spencer-uk/DubaiXTClone/pictures/image_005.jpg

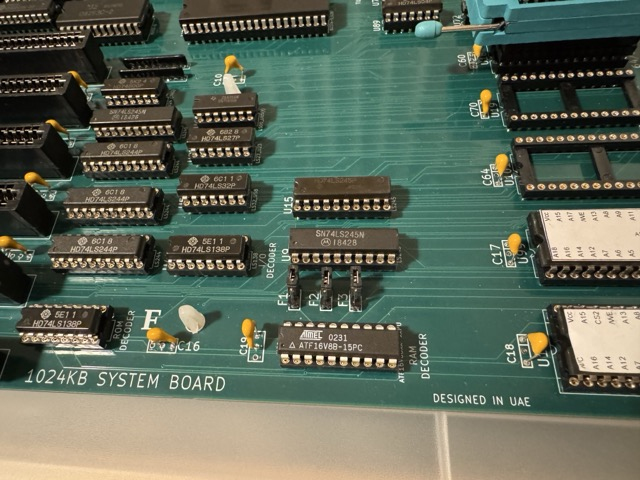
pictures/image_005.jpg
