spencer-uk/DubaiXTClone/pictures/image_008.jpg

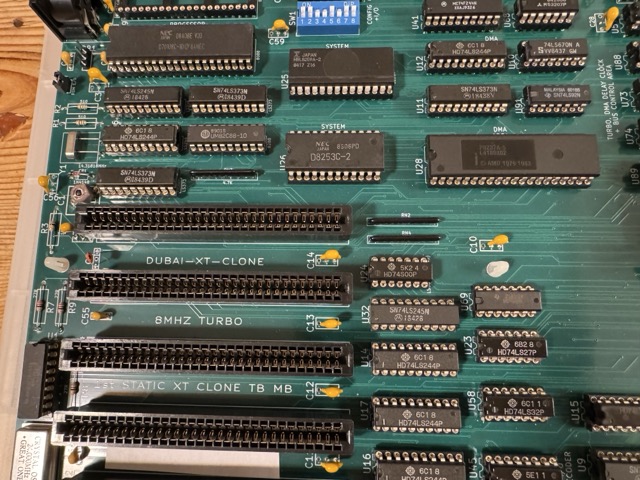
pictures/image_008.jpg
