spencer-uk/DubaiXTClone/pictures/image_012.jpg

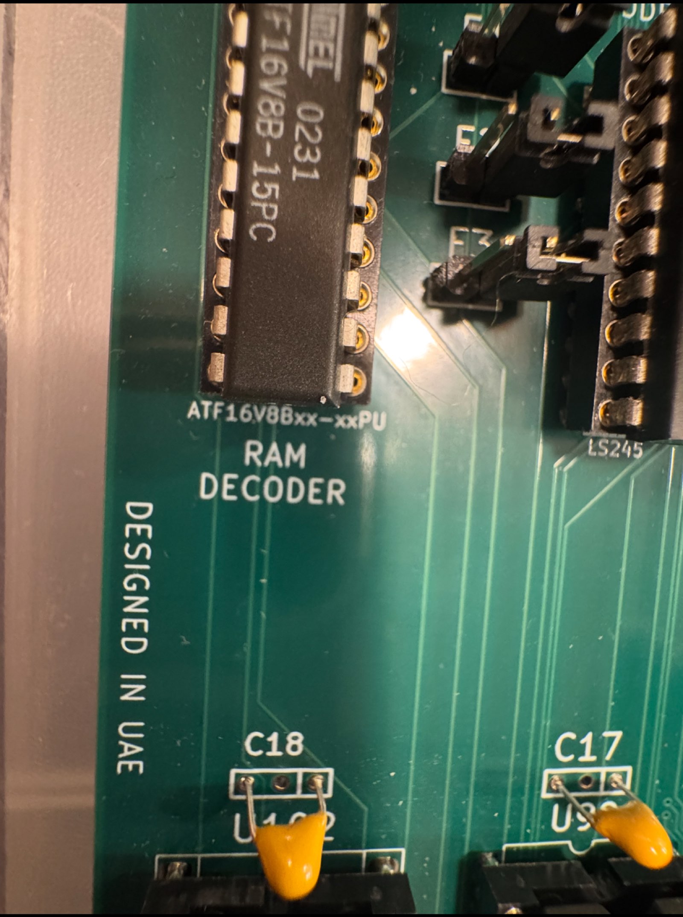
pictures/image_012.jpg
